AndrewPrimi/Group-5/Deliverable7/ohmmeter.py

"""
ohmmeter.py
Wrapper helpers for ohmmeter operation.
"""

from sar_logic import SAR_ADC

print("USING ohmmeter.py FROM:", __file__)

OHMMETER_VREF = 3.3
R_KNOWN = 1000.0


def read_ohmmeter_value(sar: SAR_ADC,
                        vref: float = OHMMETER_VREF,
                        r_known: float = R_KNOWN):
    print(f"[DEBUG] read_ohmmeter_value called with vref={vref}, r_known={r_known}")
    return sar.read_ohms(vref, r_known)
